SeeedJP/ReButton/img/13.png

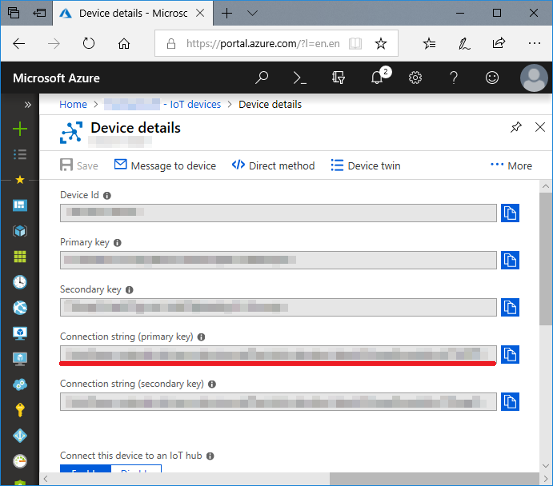
img/13.png
