SeeedJP/ReButton/img/16.png

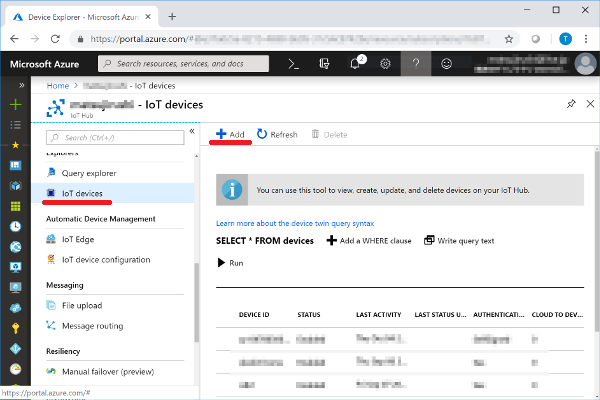
img/16.png
