SeeedJP/ReButton/img/17.png

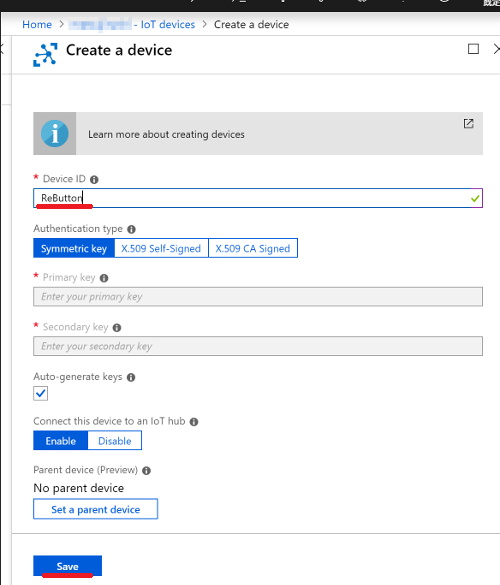
img/17.png
