SeeedJP/ReButton/img/create_hub.png

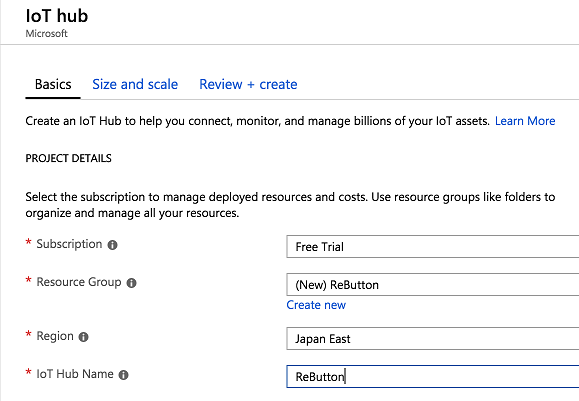
img/create_hub.png
