SeeedJP/ReButton/img/ja/8.png

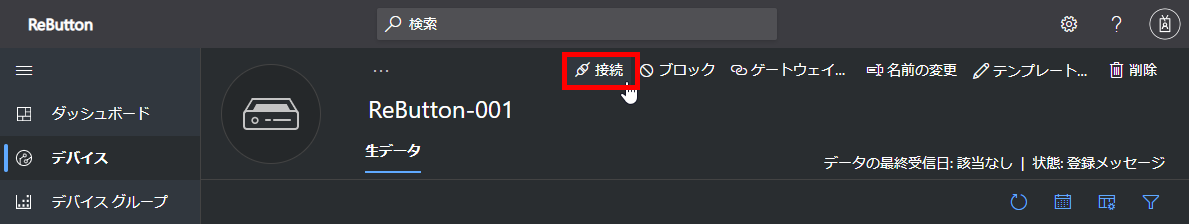
img/ja/8.png
