SeeedJP/ReButton/img/ja/9.png

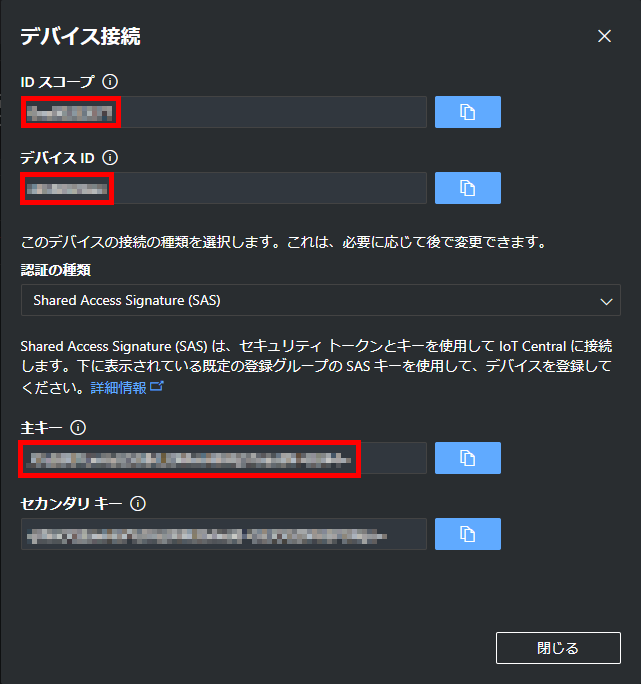
img/ja/9.png
