SeeedJP/ReButton/img/ja/10.png

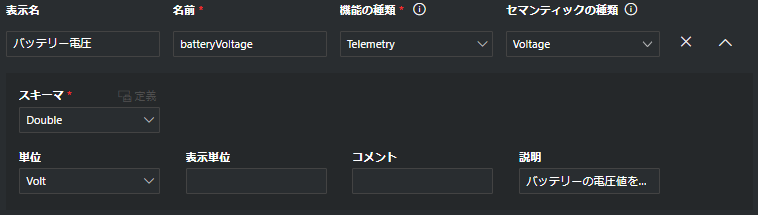
img/ja/10.png
