SeeedJP/ReButton/img/ja/11.png

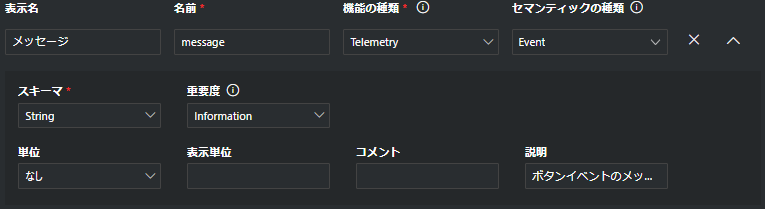
img/ja/11.png
