SeeedJP/ReButton/img/ja/18.png

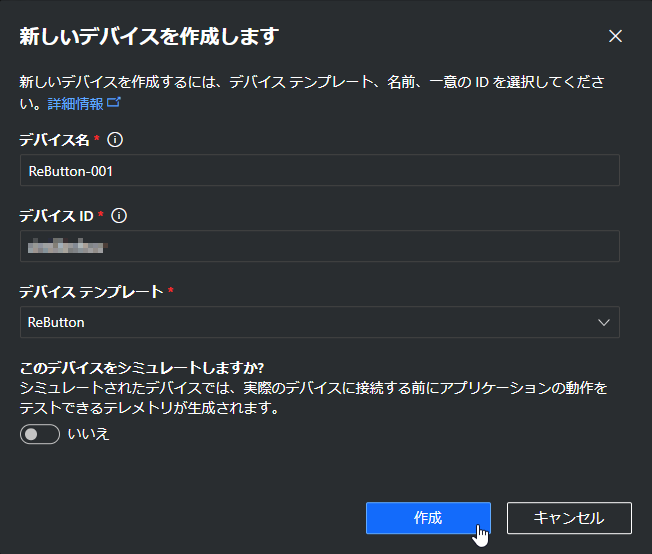
img/ja/18.png
