SeeedJP/ReButton/img/ja/boards_manager.png

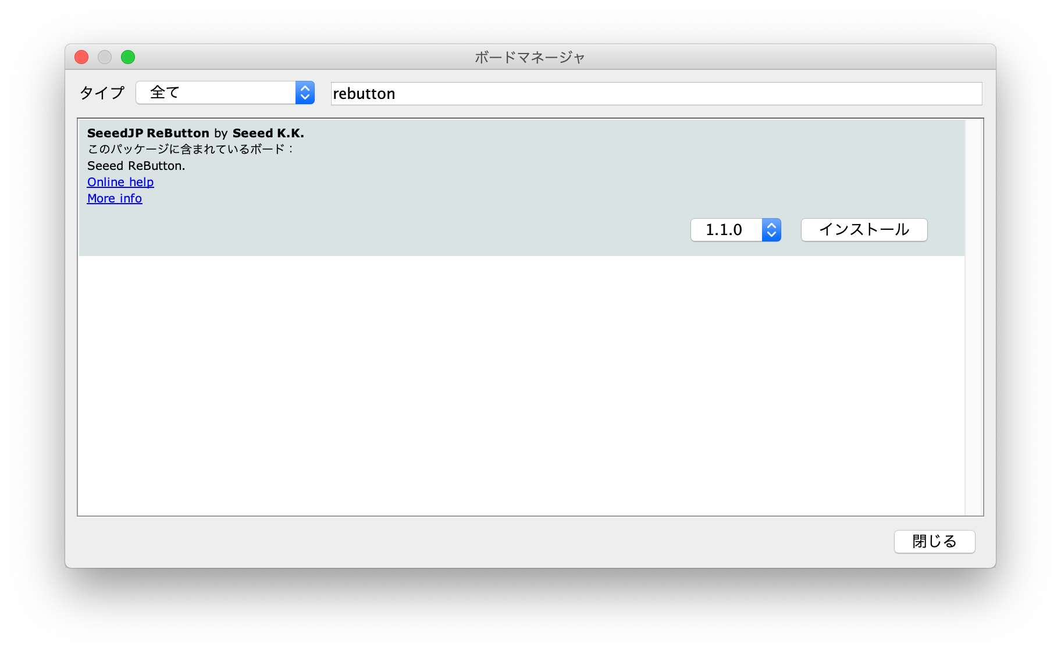
img/ja/boards_manager.png
