SeeedJP/ReButton/img/ja/ide_preference.png

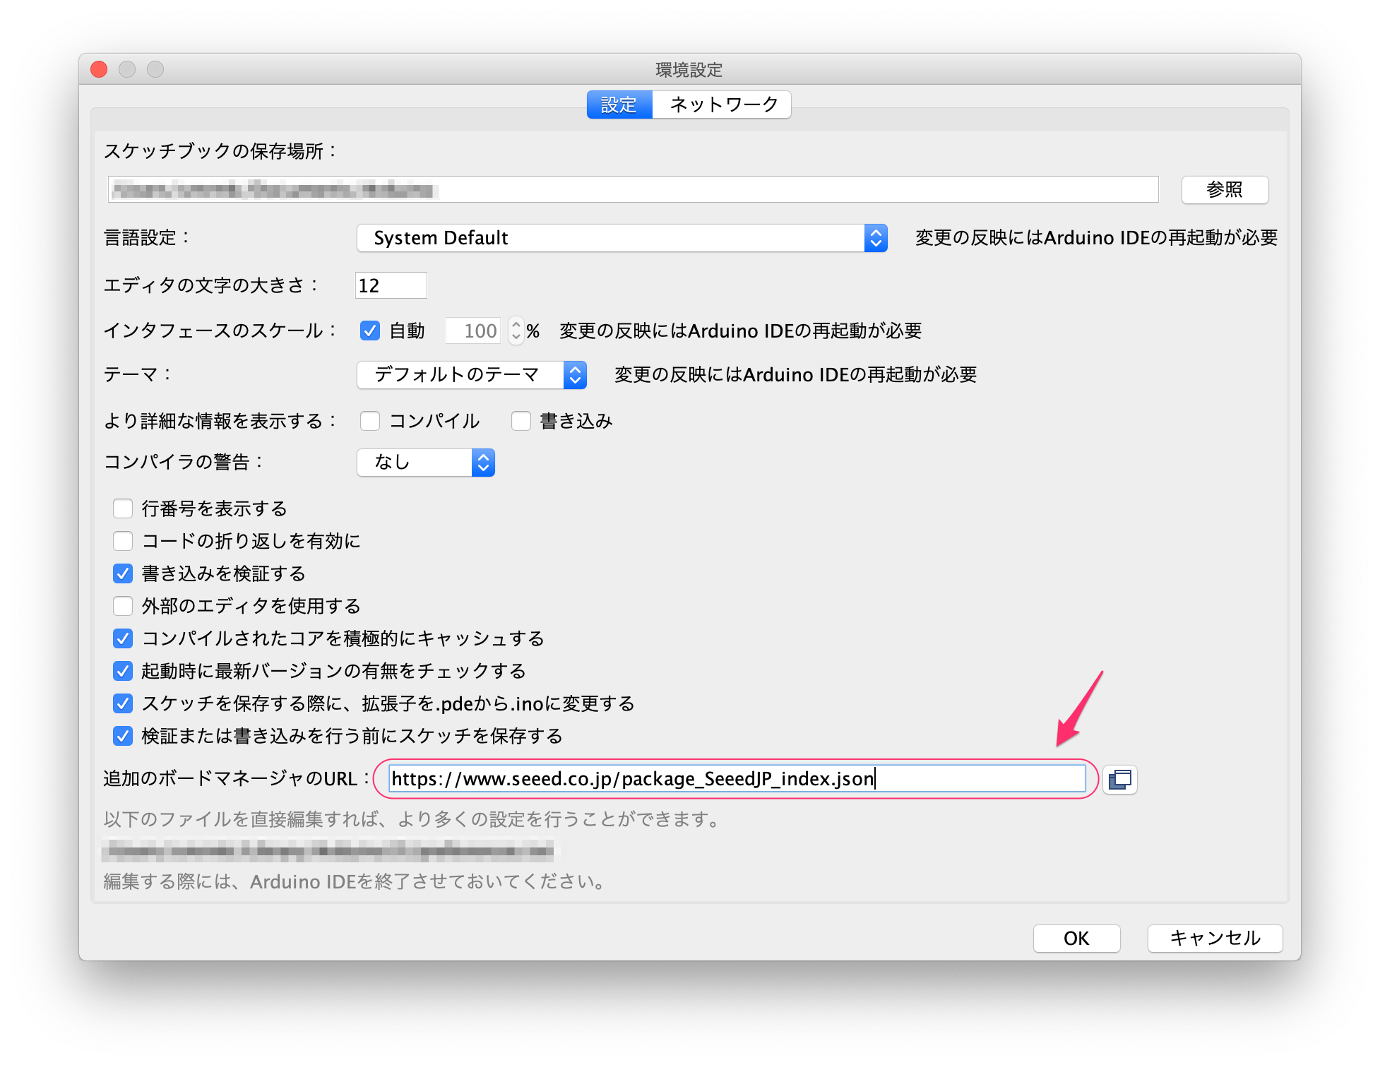
img/ja/ide_preference.png
