SeeedJP/ReButton/img/no_hub.png

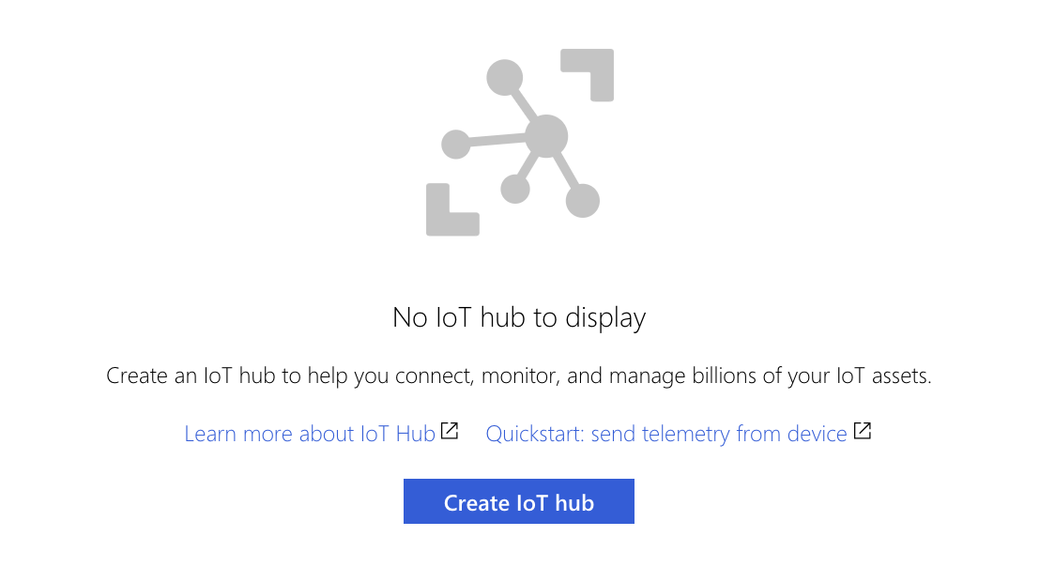
img/no_hub.png
