SeeedJP/ReButton/img/search_iot.png

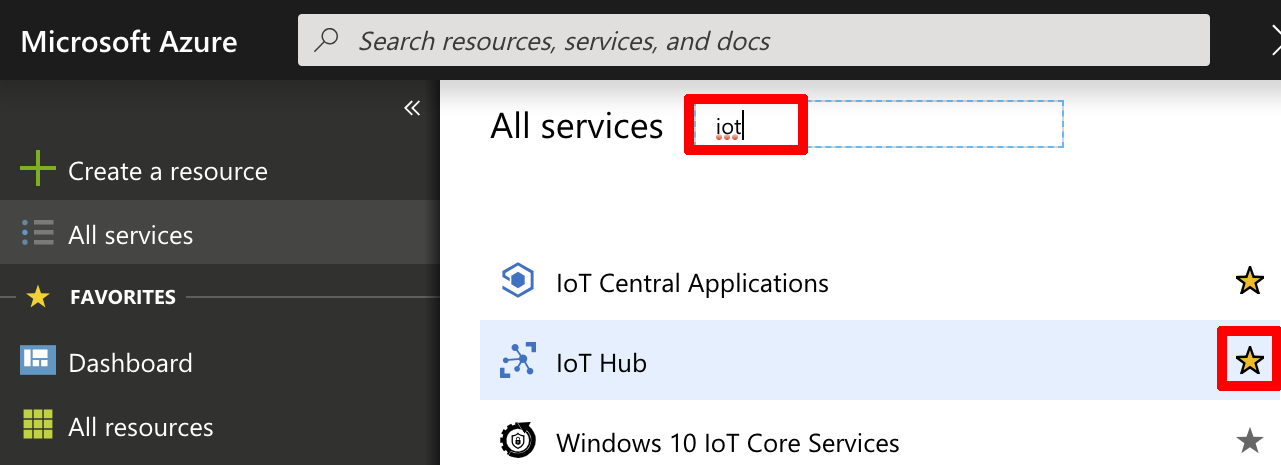
img/search_iot.png
